lloydrichards/mimirOpen/03 Software/examples/SHT31/SHT31.cpp

/*************************************************** 
  This is an example for the SHT31-D Humidity & Temp Sensor

  Designed specifically to work with the SHT31-D sensor from Adafruit
  ----> https://www.adafruit.com/products/2857

  These sensors use I2C to communicate, 2 pins are required to  
  interface
 ****************************************************/

#include <Arduino.h>
#include <Wire.h>
#include "Adafruit_SHT31.h"

bool enableHeater = false;
uint8_t loopCnt = 0;

Adafruit_SHT31 sht31 = Adafruit_SHT31();

void setup()
{
    Serial.begin(115200);

    while (!Serial)
        delay(10); // will pause Zero, Leonardo, etc until serial console opens

    Serial.println("SHT31 test");
    if (!sht31.begin(0x45))
    { // Set to 0x45 for alternate i2c addr
        Serial.println("Couldn't find SHT31");
        while (1)
            delay(1);
    }

    Serial.print("Heater Enabled State: ");
    if (sht31.isHeaterEnabled())
        Serial.println("ENABLED");
    else
        Serial.println("DISABLED");
}

void loop()
{
    float t = sht31.readTemperature();
    float h = sht31.readHumidity();

    if (!isnan(t))
    { // check if 'is not a number'
        Serial.print("Temp *C = ");
        Serial.print(t);
        Serial.print("\t\t");
    }
    else
    {
        Serial.println("Failed to read temperature");
    }

    if (!isnan(h))
    { // check if 'is not a number'
        Serial.print("Hum. % = ");
        Serial.println(h);
    }
    else
    {
        Serial.println("Failed to read humidity");
    }

    delay(1000);

    // Toggle heater enabled state every 30 seconds
    // An ~3.0 degC temperature increase can be noted when heater is enabled
    if (++loopCnt == 30)
    {
        enableHeater = !enableHeater;
        sht31.heater(enableHeater);
        Serial.print("Heater Enabled State: ");
        if (sht31.isHeaterEnabled())
            Serial.println("ENABLED");
        else
            Serial.println("DISABLED");

        loopCnt = 0;
    }
}
