lloydrichards/mimirOpen/03 Software/examples/pixels/pixelsTest.cpp

// NeoPixelTest
// This example will cycle between showing four pixels as Red, Green, Blue, White
// and then showing those pixels as Black.
//
// Included but commented out are examples of configuring a NeoPixelBus for
// different color order including an extra white channel, different data speeds, and
// for Esp8266 different methods to send the data.
// NOTE: You will need to make sure to pick the one for your platform
//
//
// There is serial output of the current state so you can confirm and follow along
//
#include <Arduino.h>
#include <NeoPixelBus.h>

const uint16_t PixelCount = 5; // this example assumes 4 pixels, making it smaller will cause a failure
const uint8_t PixelPin = 33;   // make sure to set this to the correct pin, ignored for Esp8266

#define colorSaturation 128

// three element pixels, in different order and speeds
NeoPixelBus<NeoGrbFeature, Neo800KbpsMethod> strip(PixelCount, PixelPin);
//NeoPixelBus<NeoRgbFeature, Neo400KbpsMethod> strip(PixelCount, PixelPin);

// For Esp8266, the Pin is omitted and it uses GPIO3 due to DMA hardware use.
// There are other Esp8266 alternative methods that provide more pin options, but also have
// other side effects.
// for details see wiki linked here https://github.com/Makuna/NeoPixelBus/wiki/ESP8266-NeoMethods

// You can also use one of these for Esp8266,
// each having their own restrictions
//
// These two are the same as above as the DMA method is the default
// NOTE: These will ignore the PIN and use GPI03 pin
//NeoPixelBus<NeoGrbFeature, NeoEsp8266Dma800KbpsMethod> strip(PixelCount, PixelPin);
//NeoPixelBus<NeoRgbFeature, NeoEsp8266Dma400KbpsMethod> strip(PixelCount, PixelPin);

// Uart method is good for the Esp-01 or other pin restricted modules
// for details see wiki linked here https://github.com/Makuna/NeoPixelBus/wiki/ESP8266-NeoMethods
// NOTE: These will ignore the PIN and use GPI02 pin
//NeoPixelBus<NeoGrbFeature, NeoEsp8266Uart1800KbpsMethod> strip(PixelCount, PixelPin);
//NeoPixelBus<NeoRgbFeature, NeoEsp8266Uart1400KbpsMethod> strip(PixelCount, PixelPin);

// The bitbang method is really only good if you are not using WiFi features of the ESP
// It works with all but pin 16
//NeoPixelBus<NeoGrbFeature, NeoEsp8266BitBang800KbpsMethod> strip(PixelCount, PixelPin);
//NeoPixelBus<NeoRgbFeature, NeoEsp8266BitBang400KbpsMethod> strip(PixelCount, PixelPin);

// four element pixels, RGBW
//NeoPixelBus<NeoRgbwFeature, Neo800KbpsMethod> strip(PixelCount, PixelPin);

RgbColor red(colorSaturation, 0, 0);
RgbColor green(0, colorSaturation, 0);
RgbColor blue(0, 0, colorSaturation);
RgbColor white(colorSaturation);
RgbColor black(0);

HslColor hslRed(red);
HslColor hslGreen(green);
HslColor hslBlue(blue);
HslColor hslWhite(white);
HslColor hslBlack(black);

void setup()
{
    Serial.begin(115200);
    while (!Serial)
        ; // wait for serial attach

    Serial.println();
    Serial.println("Initializing...");
    Serial.flush();

    pinMode(32, LOW); //Set the NPN on

    // this resets all the neopixels to an off state
    strip.Begin();
    strip.Show();

    Serial.println();
    Serial.println("Running...");
}

void loop()
{
    delay(5000);

    Serial.println("Colors R, G, B, W...");

    // set the colors,
    // if they don't match in order, you need to use NeoGrbFeature feature
    strip.SetPixelColor(0, red);
    strip.SetPixelColor(1, green);
    strip.SetPixelColor(2, blue);
    strip.SetPixelColor(3, white);
    strip.SetPixelColor(4, red);
    // the following line demonstrates rgbw color support
    // if the NeoPixels are rgbw types the following line will compile
    // if the NeoPixels are anything else, the following line will give an error
    //strip.SetPixelColor(3, RgbwColor(colorSaturation));
    strip.Show();

    delay(5000);

    Serial.println("Off ...");

    // turn off the pixels
    strip.SetPixelColor(0, black);
    strip.SetPixelColor(1, black);
    strip.SetPixelColor(2, black);
    strip.SetPixelColor(3, black);
    strip.SetPixelColor(4, black);
    strip.Show();

    delay(5000);

    Serial.println("HSL Colors R, G, B, W...");

    // set the colors,
    // if they don't match in order, you may need to use NeoGrbFeature feature
    strip.SetPixelColor(0, hslRed);
    strip.SetPixelColor(1, hslGreen);
    strip.SetPixelColor(2, hslBlue);
    strip.SetPixelColor(3, hslWhite);
    strip.SetPixelColor(4, hslBlue);
    strip.Show();

    delay(5000);

    Serial.println("Off again...");

    // turn off the pixels
    strip.SetPixelColor(0, hslBlack);
    strip.SetPixelColor(1, hslBlack);
    strip.SetPixelColor(2, hslBlack);
    strip.SetPixelColor(3, hslBlack);
    strip.SetPixelColor(4, hslBlack);
    strip.Show();
}
