lloydrichards/mimirOpen/03 Software/examples/LSM303/Compass.cpp

#include <Wire.h>
#include <Adafruit_Sensor.h>
#include <Adafruit_LIS2MDL.h>


Adafruit_LIS2MDL mag = Adafruit_LIS2MDL(12345);

void setup(void)
{
  Serial.begin(115200);
  Serial.println("Magnetometer Test"); Serial.println("");

  /* Initialise the sensor */
  if(!mag.begin())
  {
    /* There was a problem detecting the LIS2MDL ... check your connections */
    Serial.println("Ooops, no LIS2MDL detected ... Check your wiring!");
    while(1);
  }
}

void loop(void)
{
  /* Get a new sensor event */
  sensors_event_t event;
  mag.getEvent(&event);

  float Pi = 3.14159;

  // Calculate the angle of the vector y,x
  float heading = (atan2(event.magnetic.y,event.magnetic.x) * 180) / Pi;

  // Normalize to 0-360
  if (heading < 0)
  {
    heading = 360 + heading;
  }
  Serial.print("Compass Heading: ");
  Serial.println(heading);
  delay(500);
}
